kangkang198/HoloCubicS3/2.Firmware/HoloCubicS3(xiaozhi-esp32)/docs/atoms3r-echo-base.jpg

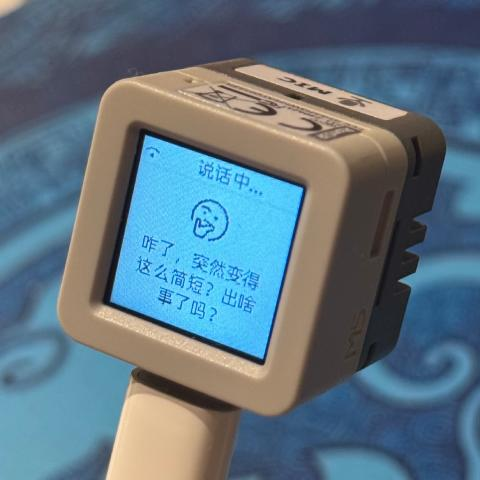
2.Firmware/HoloCubicS3(xiaozhi-esp32)/docs/atoms3r-echo-base.jpg
