kangkang198/HoloCubicS3/2.Firmware/HoloCubicS3(xiaozhi-esp32)/docs/esp32s3-box3.jpg

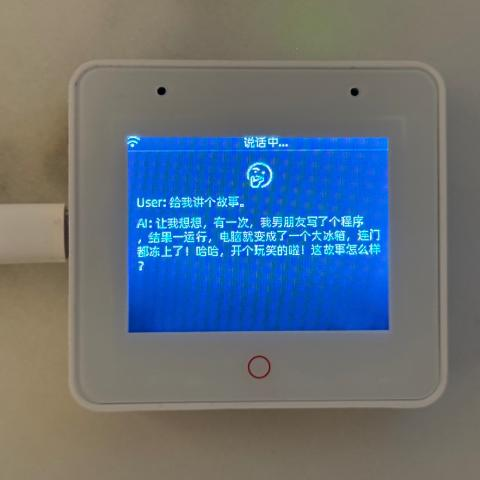
2.Firmware/HoloCubicS3(xiaozhi-esp32)/docs/esp32s3-box3.jpg
