kangkang198/HoloCubicS3/2.Firmware/HoloCubicS3(xiaozhi-esp32)/docs/m5stack-cores3.jpg

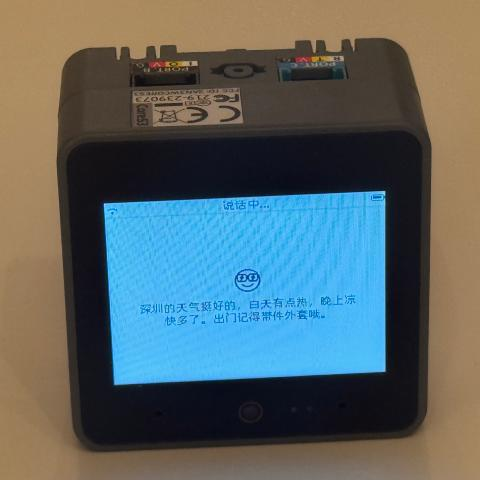
2.Firmware/HoloCubicS3(xiaozhi-esp32)/docs/m5stack-cores3.jpg
