kangkang198/HoloCubicS3/2.Firmware/HoloCubicS3(xiaozhi-esp32)/docs/magiclick-2p4.jpg

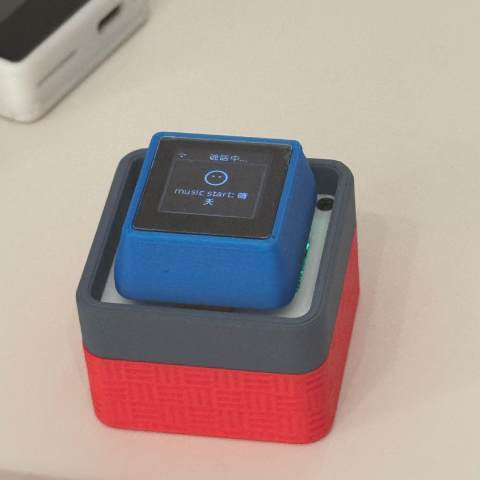
2.Firmware/HoloCubicS3(xiaozhi-esp32)/docs/magiclick-2p4.jpg
