kangkang198/HoloCubicS3/2.Firmware/HoloCubicS3(xiaozhi-esp32)/docs/v1/atoms3r.jpg

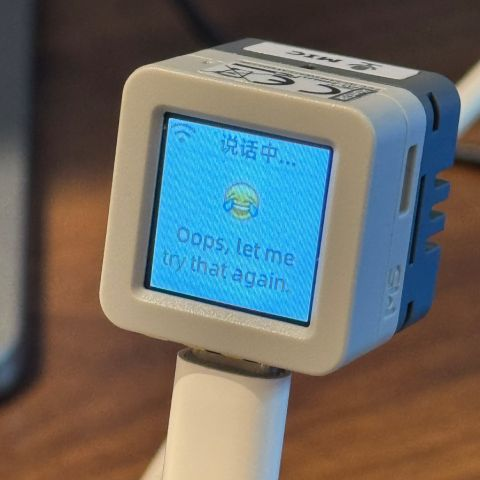
2.Firmware/HoloCubicS3(xiaozhi-esp32)/docs/v1/atoms3r.jpg
