kangkang198/HoloCubicS3/2.Firmware/HoloCubicS3(xiaozhi-esp32)/docs/v1/lichuang-s3.jpg

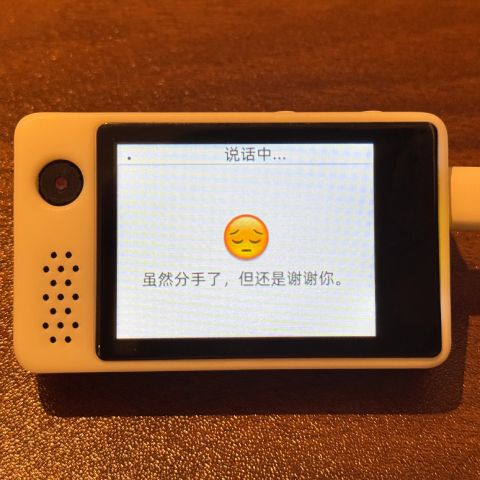
2.Firmware/HoloCubicS3(xiaozhi-esp32)/docs/v1/lichuang-s3.jpg
