kangkang198/HoloCubicS3/2.Firmware/HoloCubicS3(xiaozhi-esp32)/docs/waveshare-esp32-s3-touch-amoled-1.8.jpg

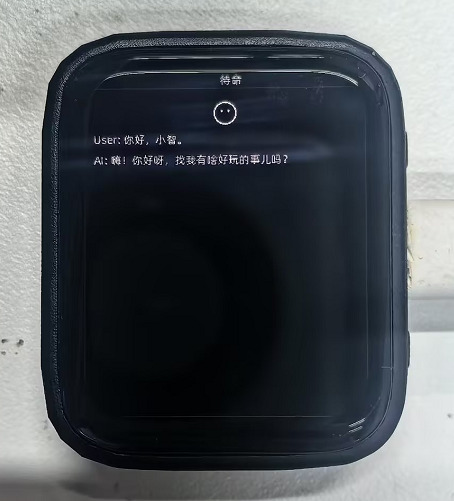
2.Firmware/HoloCubicS3(xiaozhi-esp32)/docs/waveshare-esp32-s3-touch-amoled-1.8.jpg
