kangkang198/HoloCubicS3/2.Firmware/HoloCubicS3(xiaozhi-esp32)/docs/xmini-c3.jpg

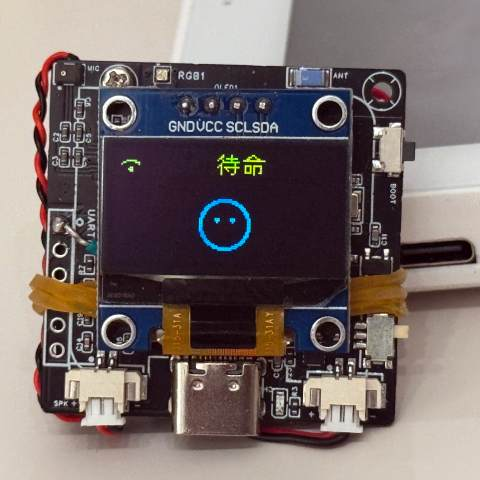
2.Firmware/HoloCubicS3(xiaozhi-esp32)/docs/xmini-c3.jpg
