kangkang198/HoloCubicS3/2.Firmware/HoloCubicS3(xiaozhi-esp32)/scripts/p3_tools/img/img.png

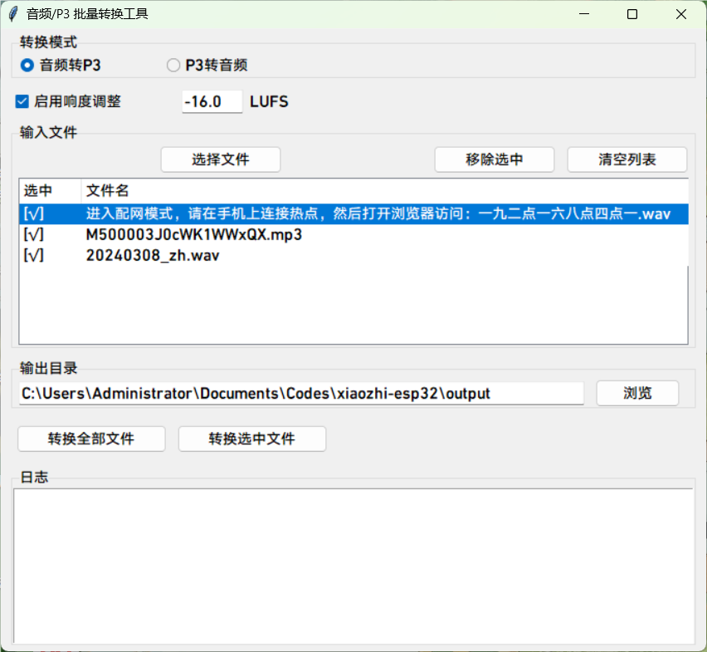
2.Firmware/HoloCubicS3(xiaozhi-esp32)/scripts/p3_tools/img/img.png
